AwesDea/SmartLab/Document/Pic/Arduino Uno - Datasheet.jpg

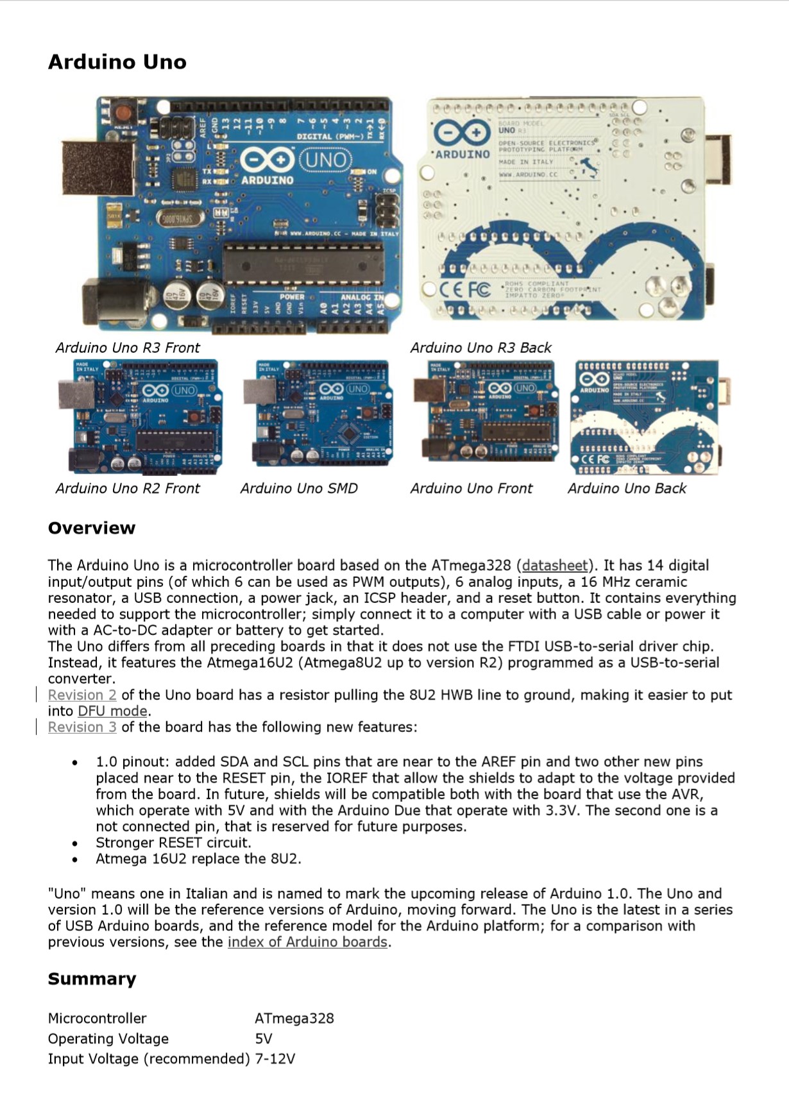
Document/Pic/Arduino Uno - Datasheet.jpg
