AwesDea/SmartLab/Document/Pic/Camera.jpg

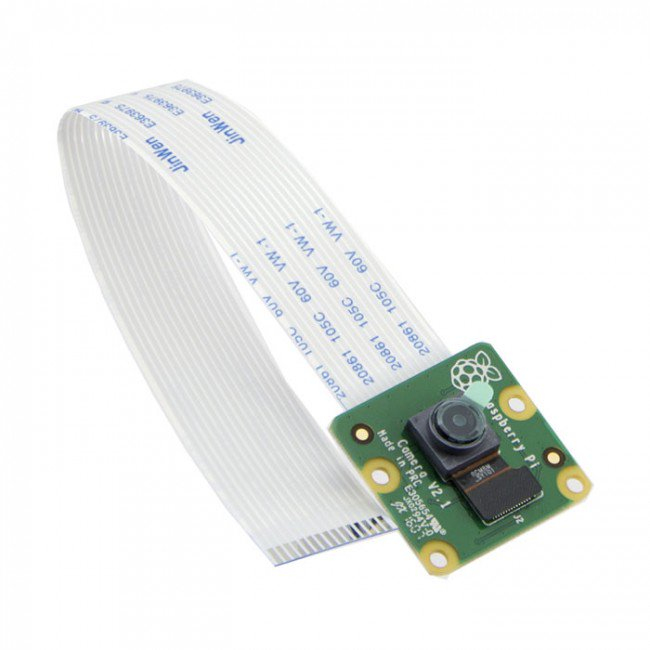
Document/Pic/Camera.jpg
