AwesDea/SmartLab/Document/Pic/DHT11 - Datasheet.jpg

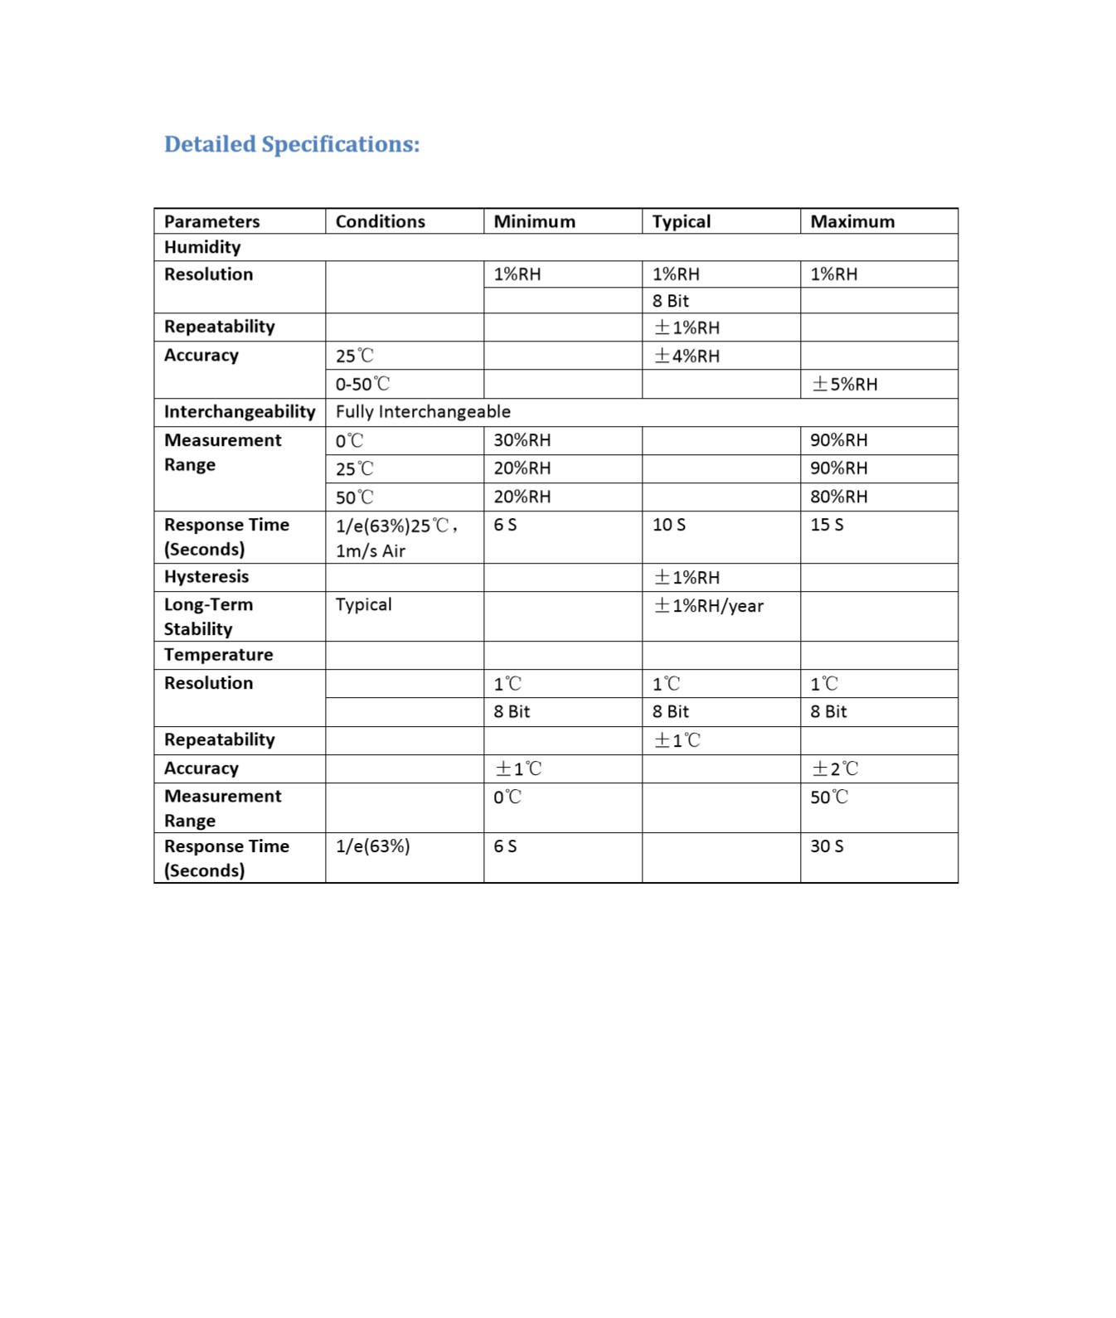
Document/Pic/DHT11 - Datasheet.jpg
