AwesDea/SmartLab/Document/Pic/ESP8266-01.jpg

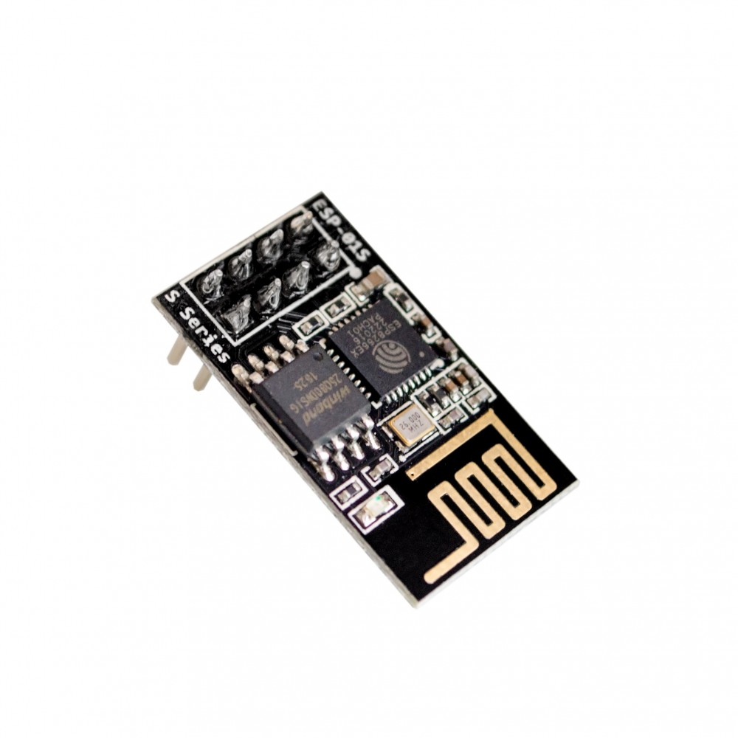
Document/Pic/ESP8266-01.jpg
