AwesDea/SmartLab/Document/Pic/ESP - Datasheet.jpg

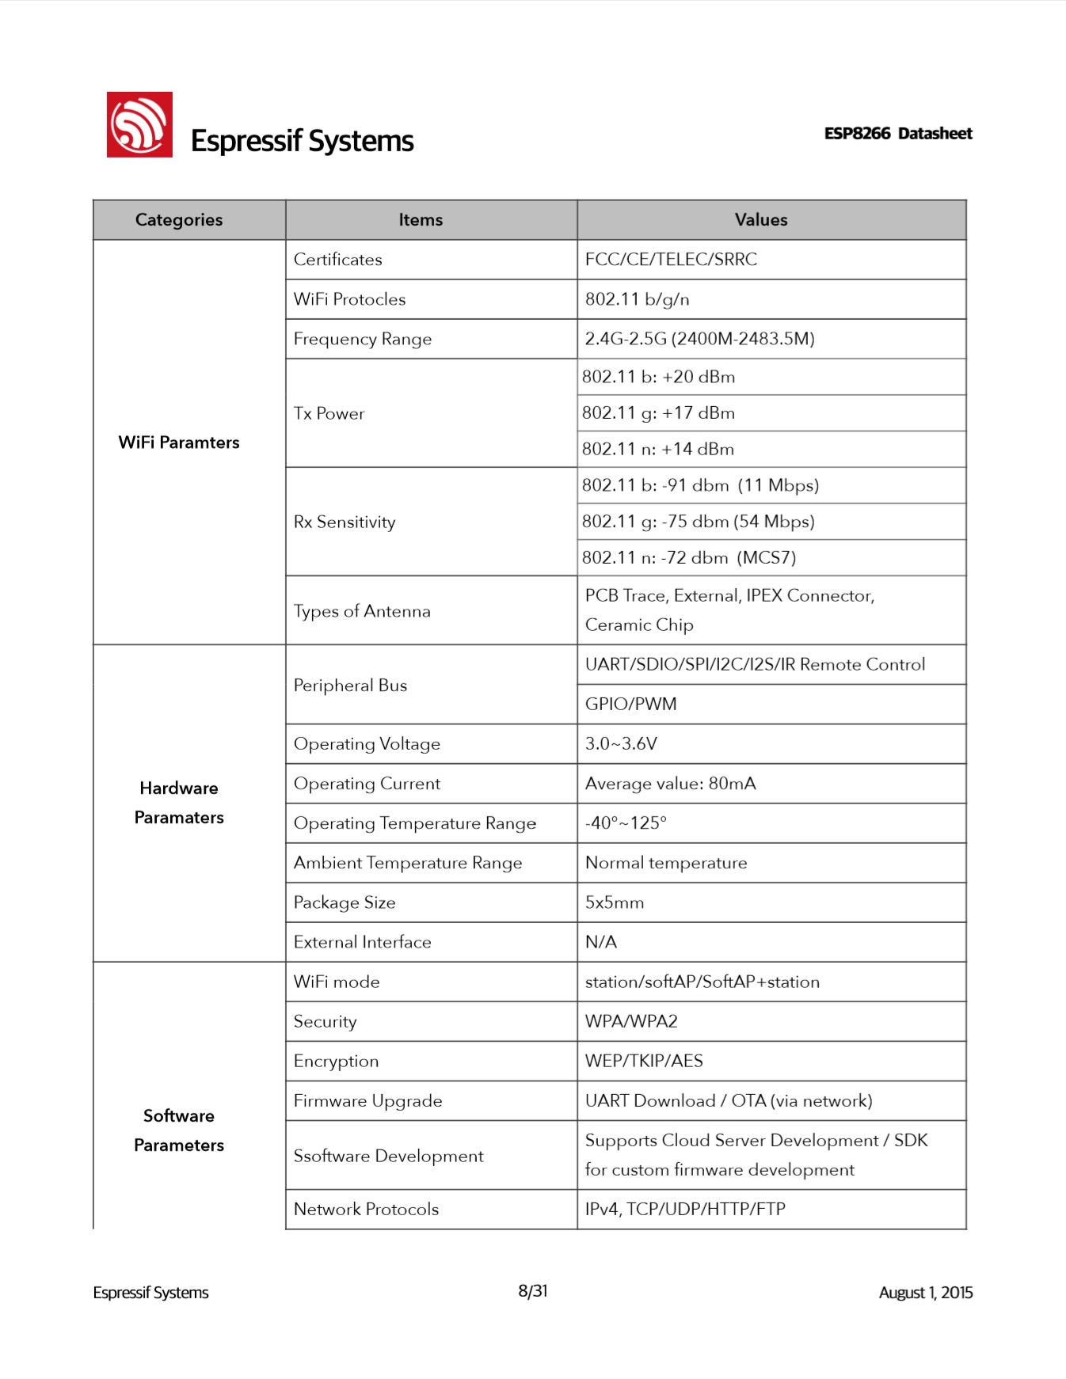
Document/Pic/ESP - Datasheet.jpg
