AwesDea/SmartLab/Document/Pic/Fan.jpg

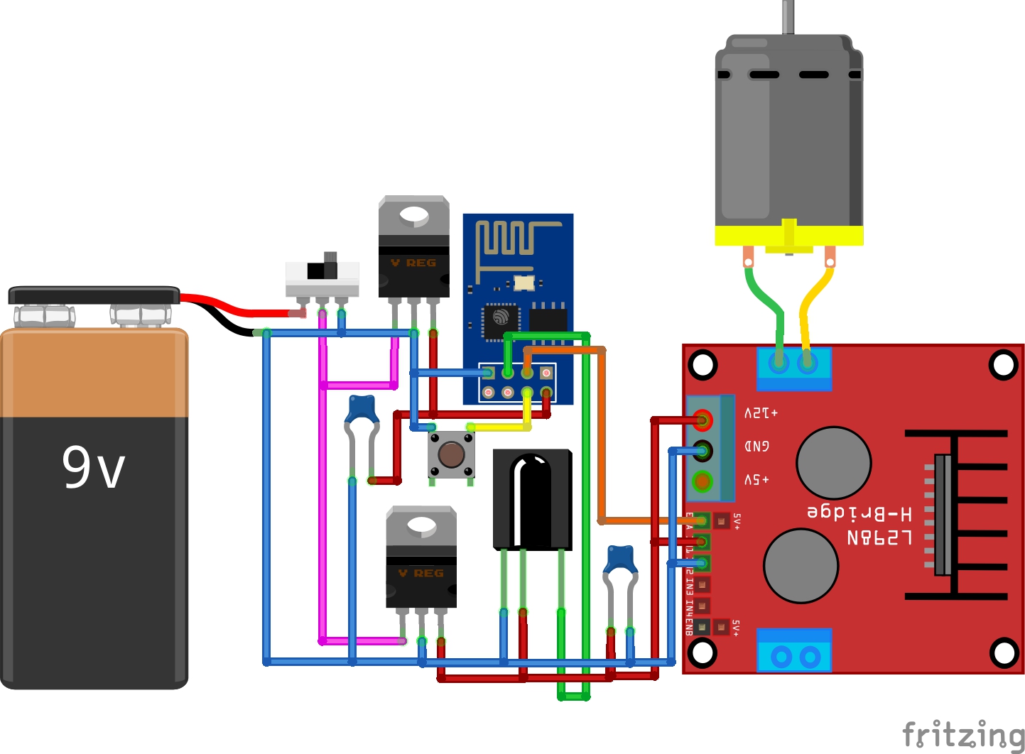
Document/Pic/Fan.jpg
