AwesDea/SmartLab/Document/Pic/IoT.png

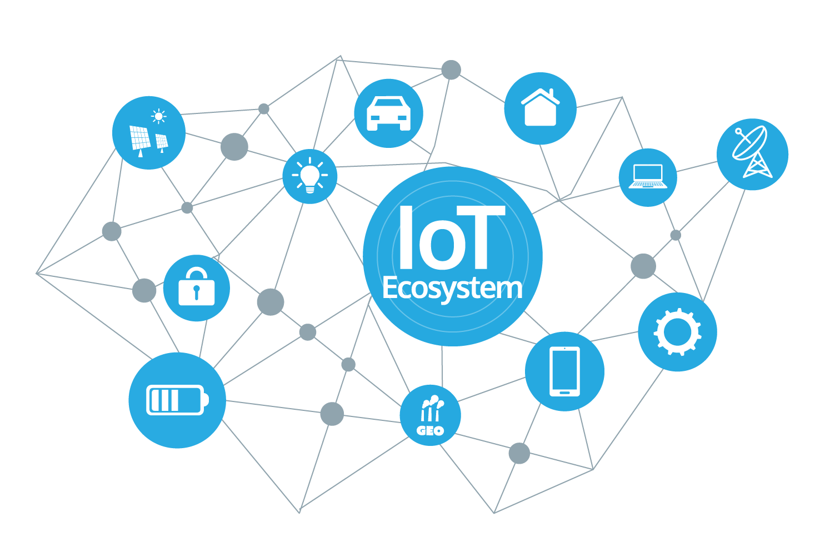
Document/Pic/IoT.png
