AwesDea/SmartLab/Document/Pic/IR - Datasheet.jpg

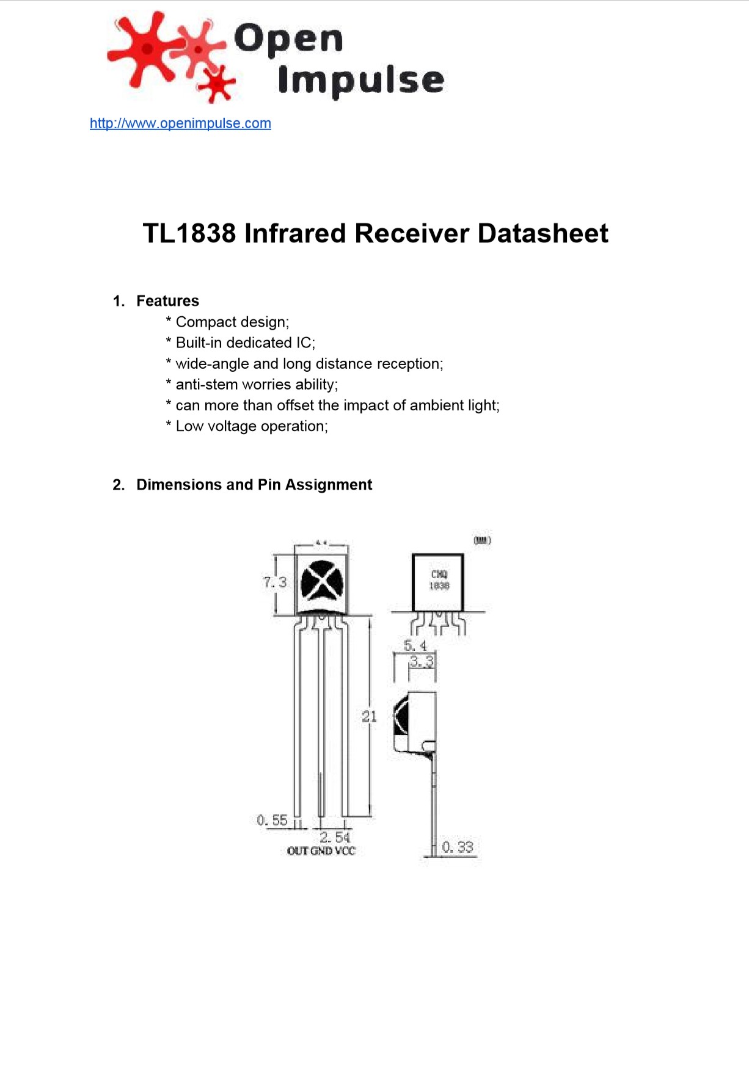
Document/Pic/IR - Datasheet.jpg
