AwesDea/SmartLab/Document/Pic/MQ9-DHT.jpg

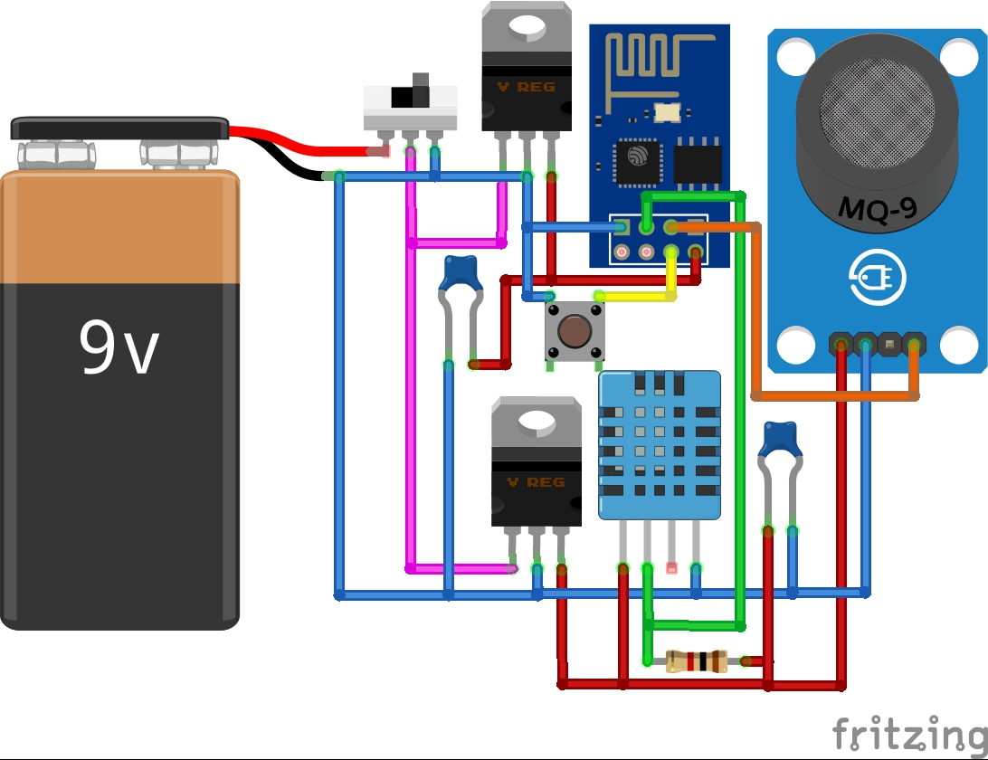
Document/Pic/MQ9-DHT.jpg
