AwesDea/SmartLab/Document/Pic/MQ9.jpg

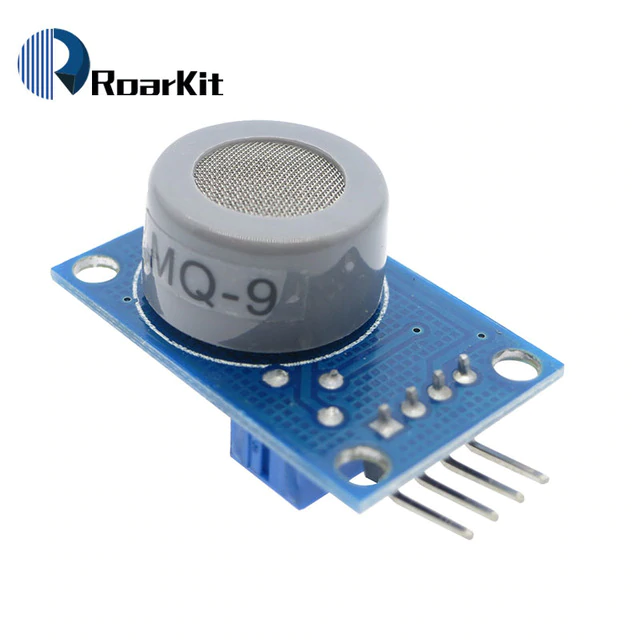
Document/Pic/MQ9.jpg
