AwesDea/SmartLab/Document/Pic/MQ-9 - Datasheet.jpg

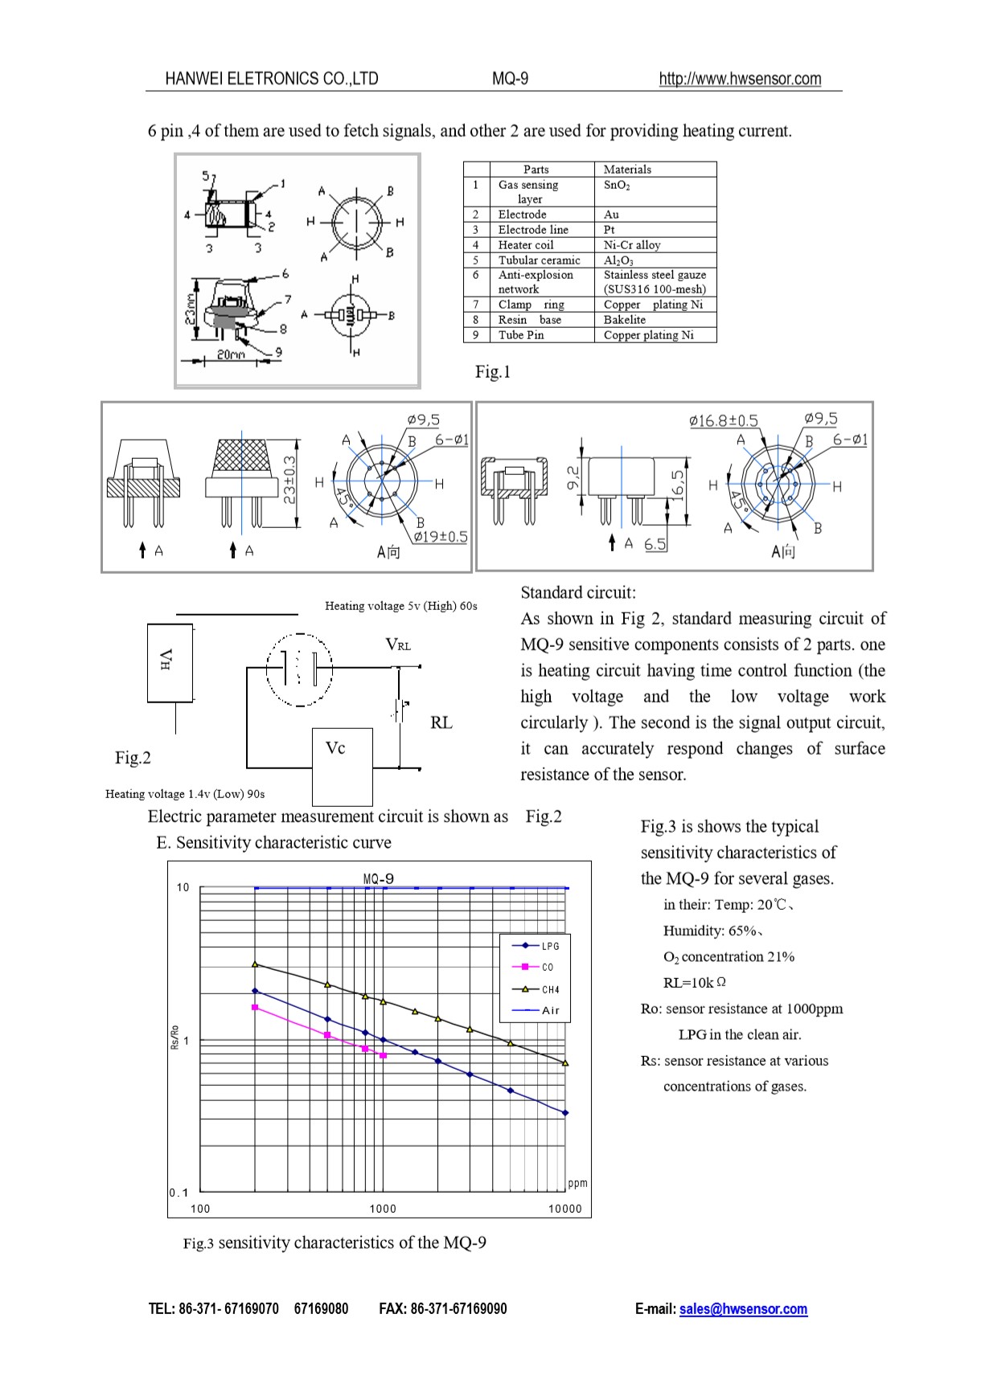
Document/Pic/MQ-9 - Datasheet.jpg
