AwesDea/SmartLab/Document/Pic/PIR - Datasheet.jpg

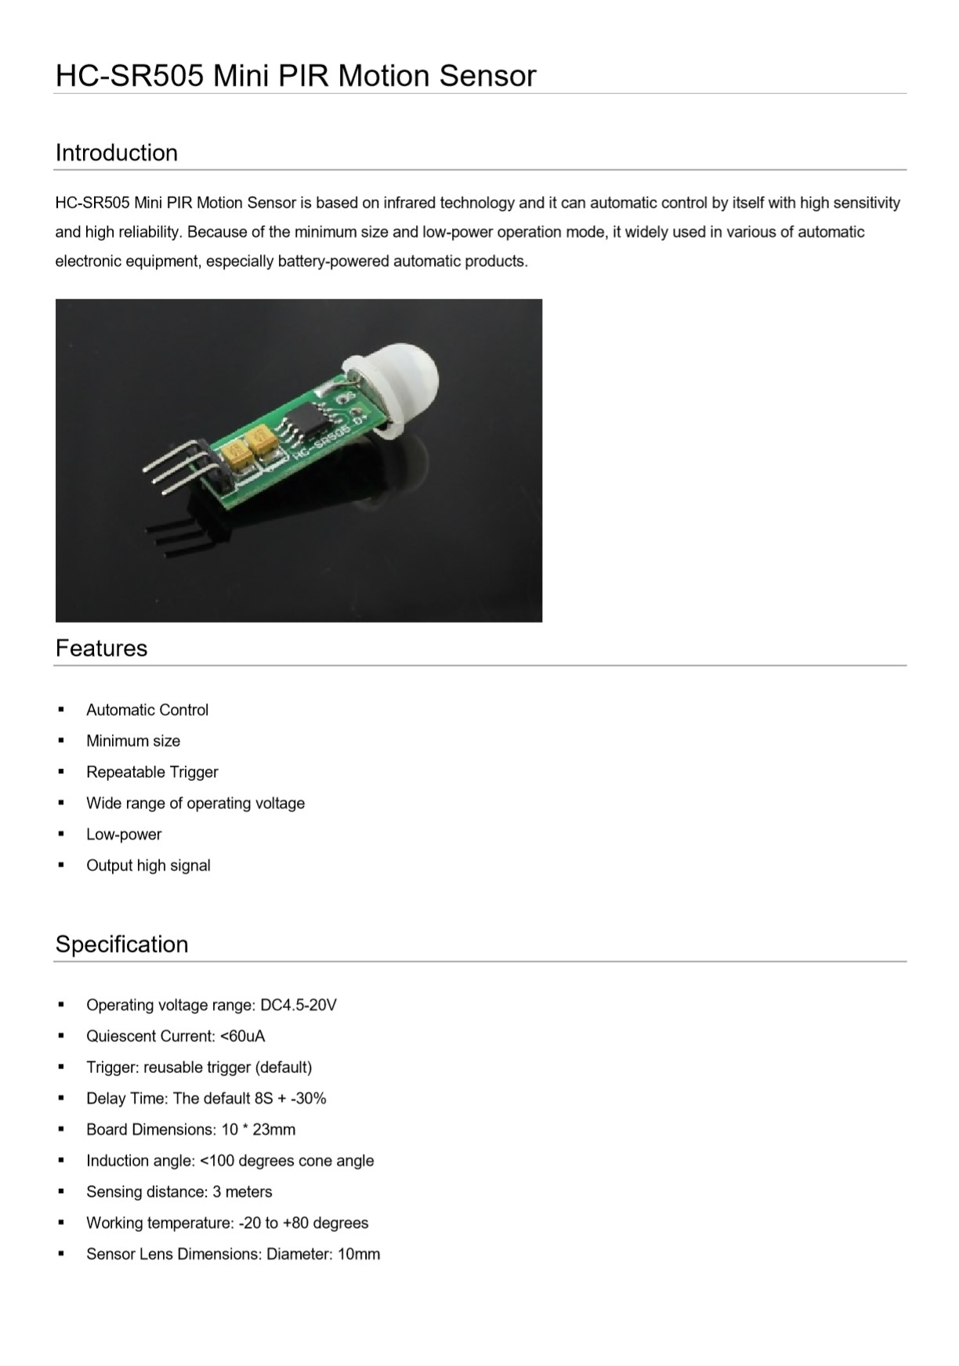
Document/Pic/PIR - Datasheet.jpg
