AwesDea/SmartLab/Document/Pic/PIR.jpg

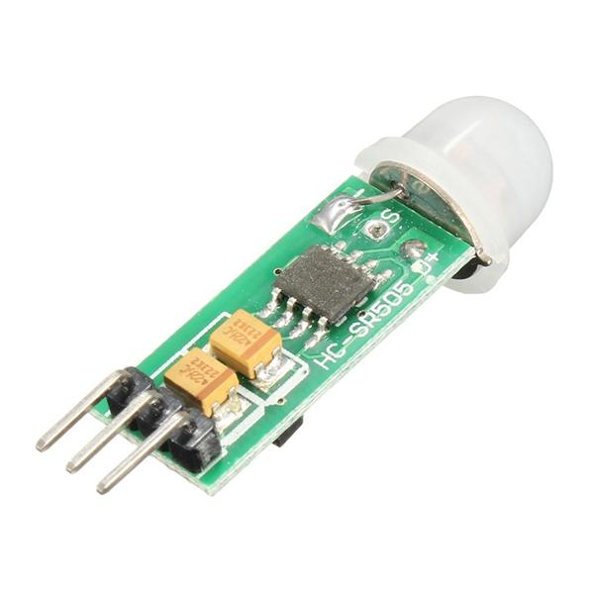
Document/Pic/PIR.jpg
