AwesDea/SmartLab/Document/Pic/Remote Control.jpg

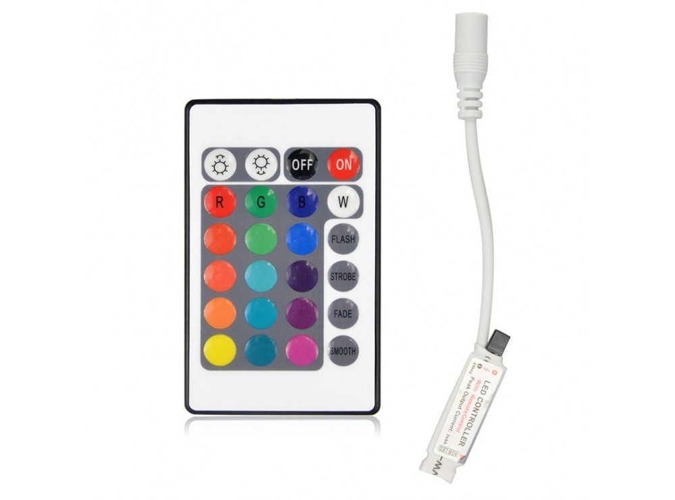
Document/Pic/Remote Control.jpg
