AwesDea/SmartLab/Document/Pic/RFID - Datasheet.jpg

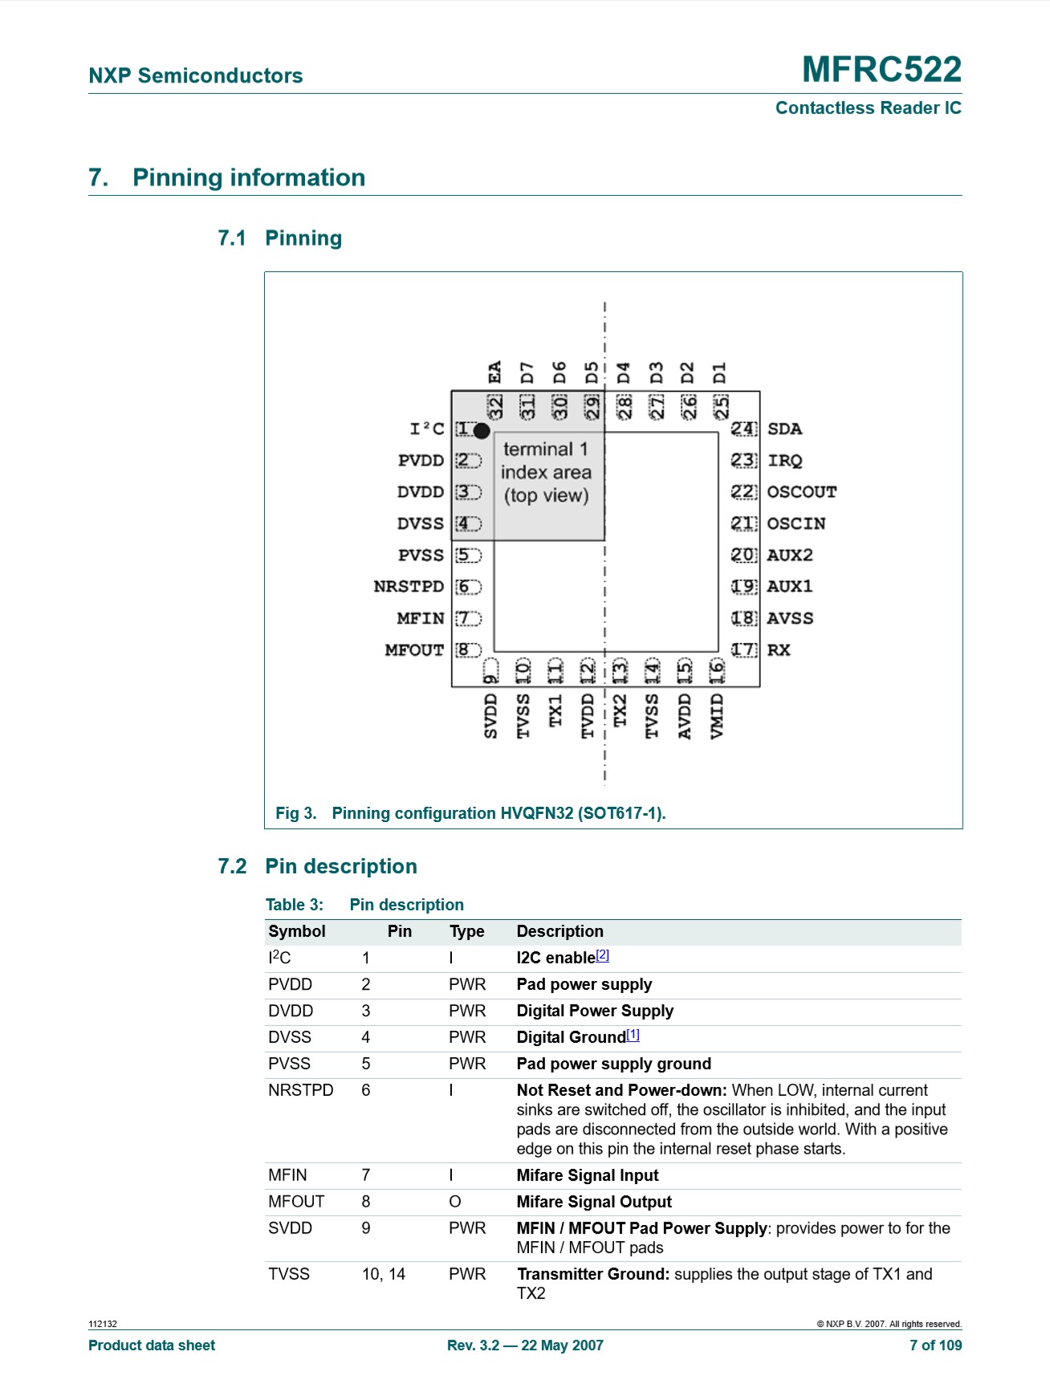
Document/Pic/RFID - Datasheet.jpg
