AwesDea/SmartLab/Document/Pic/RFID.jpg

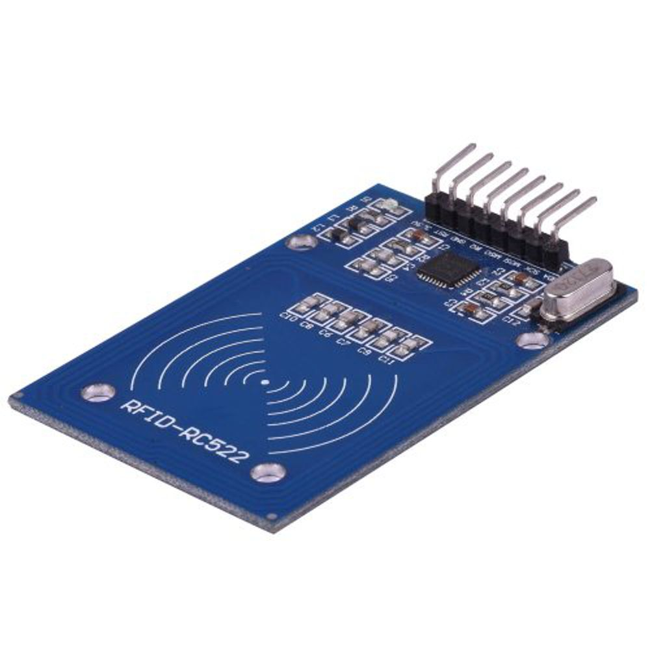
Document/Pic/RFID.jpg
