AwesDea/SmartLab/Document/Pic/RPi - Datasheet.jpg

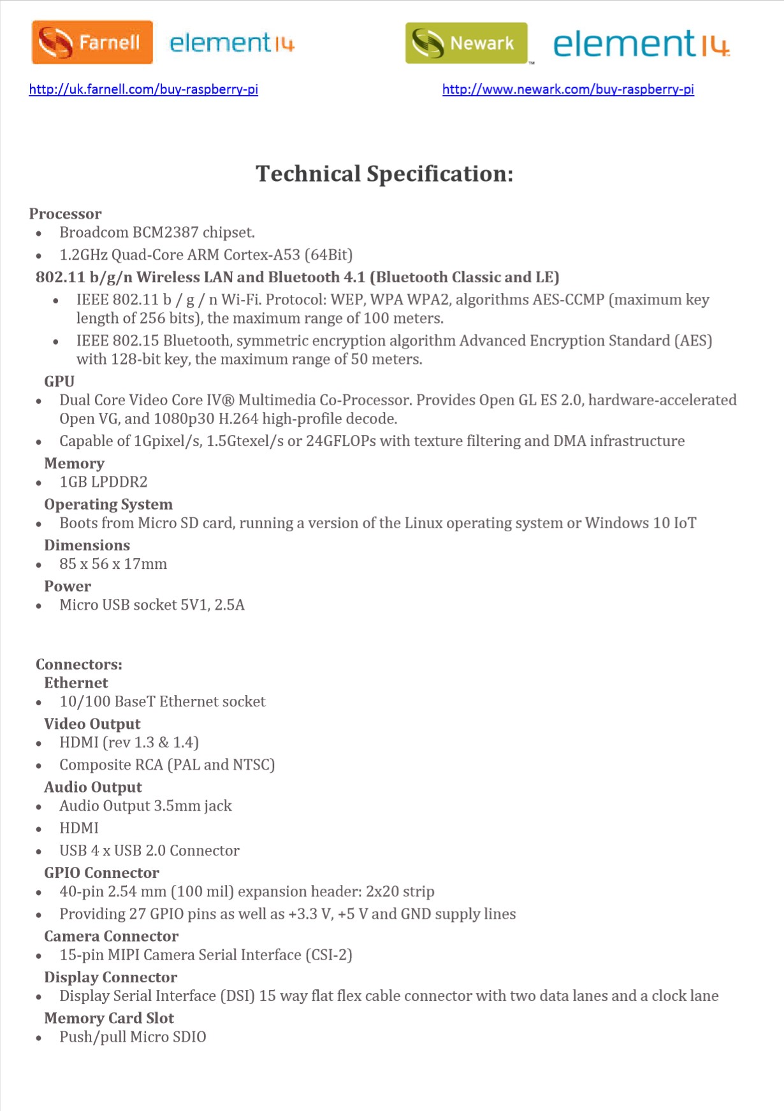
Document/Pic/RPi - Datasheet.jpg
