AwesDea/SmartLab/Document/Pic/UI.jpg

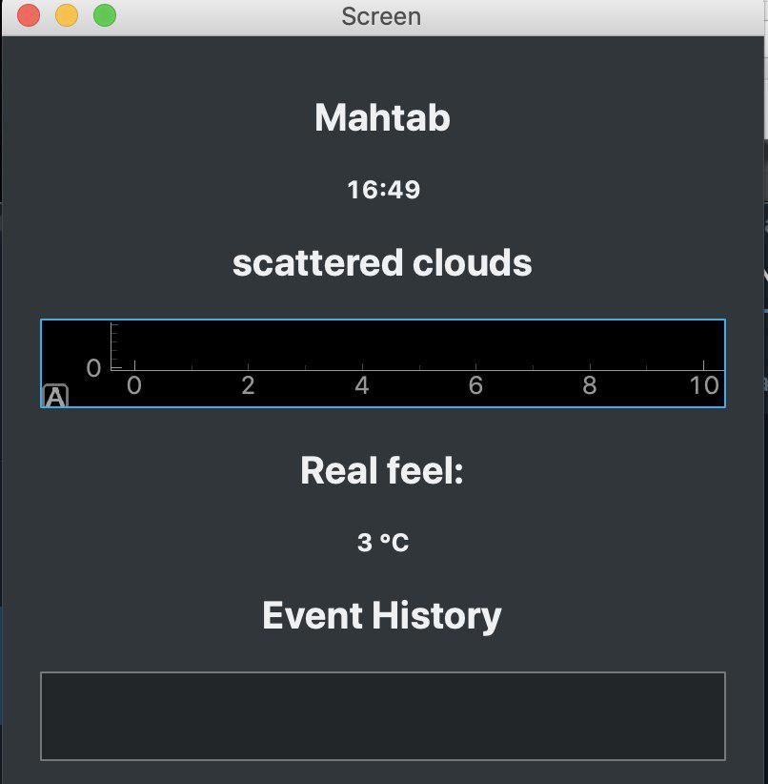
Document/Pic/UI.jpg
