AwesDea/SmartLab/Slide/Pic/ESP8266-01.jpg

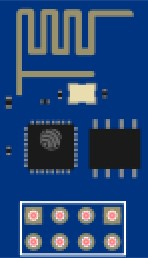
Slide/Pic/ESP8266-01.jpg
