AwesDea/SmartLab/Slide/Pic/Mirror.jpg

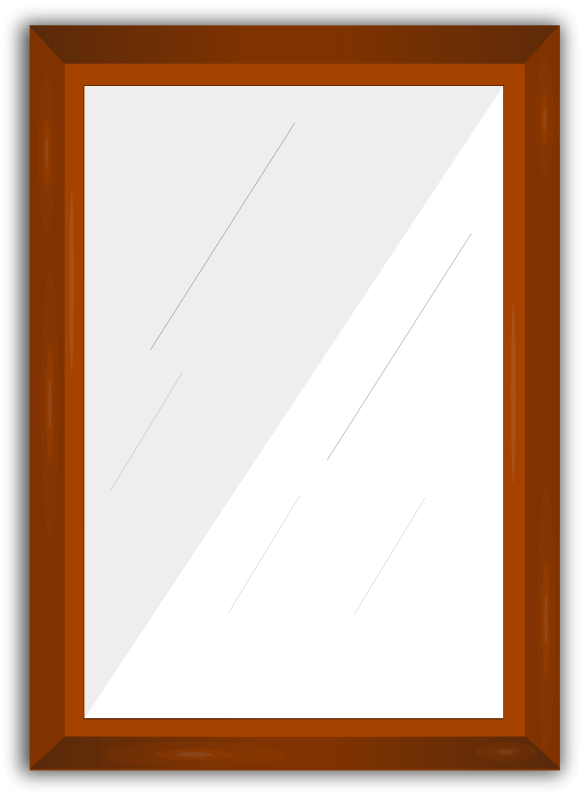
Slide/Pic/Mirror.jpg
