AwesDea/SmartLab/Slide/Pic/Modem.jpg

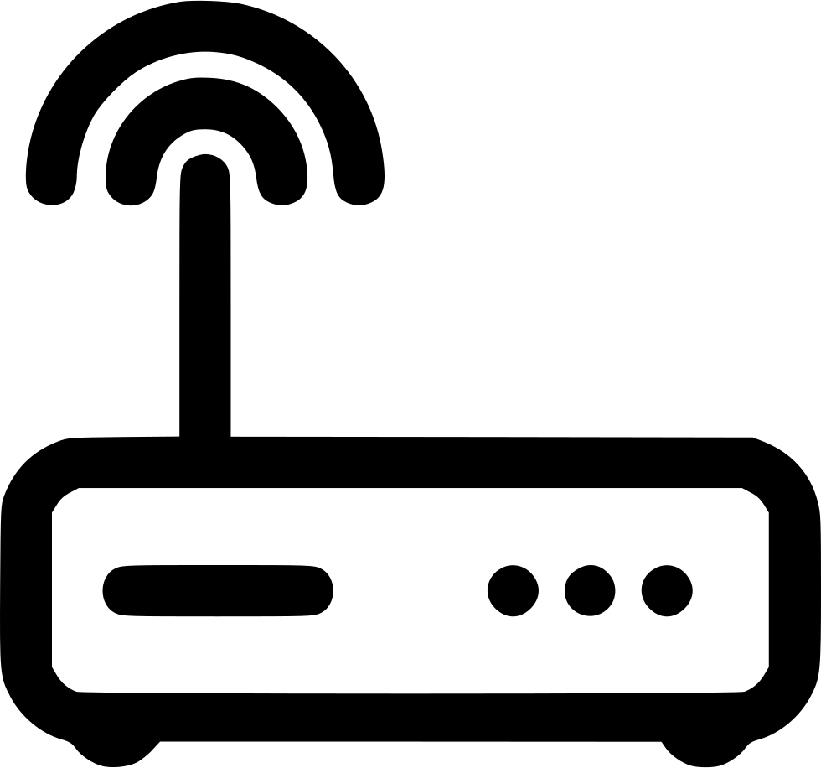
Slide/Pic/Modem.jpg
