AwesDea/SmartLab/Slide/Pic/RPi.jpg

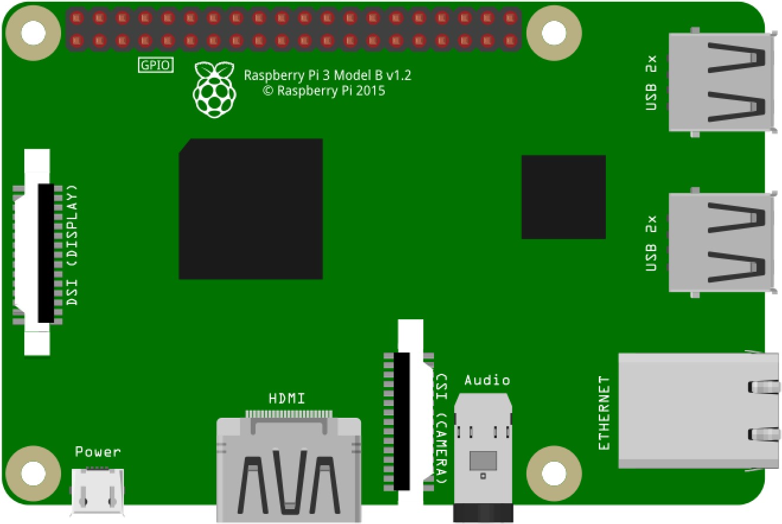
Slide/Pic/RPi.jpg
